nico25112005/Nerf-ATG-Electronics/Simulations/LTSpice/results/03.04.2026/L_6.8µH.jpg

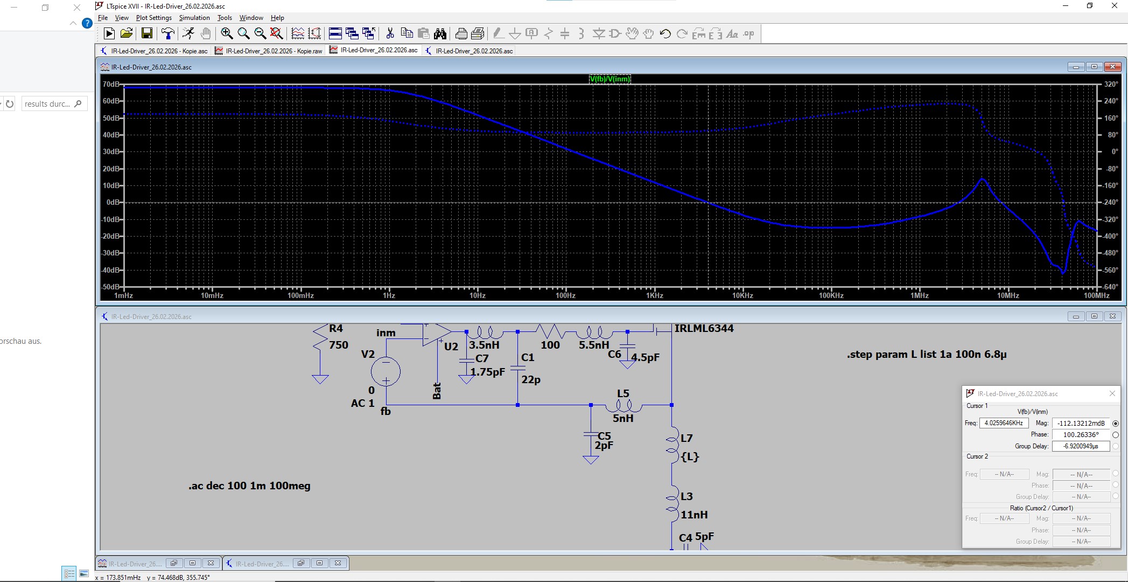
Simulations/LTSpice/results/03.04.2026/L_6.8µH.jpg
