nico25112005/Nerf-ATG-Electronics/Simulations/LTSpice/Draft2.asc

C1: cap; 22p
D1: LED; PT-121-B
M1: nmos; IRLML6344
R1: res; 1
R2: res; 100
R3: res; 1k5
R4: res; 750
R5: res; {R}
U2: opamp2; OPAx197
V1: voltage; 6
V2: voltage; PULSE(0 0.3 0 0 0 13µ 26µ)
Named nets: Bat, 0
.include C:\\Users\
icob\\OneDrive\\Dokumente\\LTspiceXVII\\lib\\custom\\OPA197\\OPAx197.LIB
.op
